ahmadtak-3212/led_cube_project/fpga/led_cube_v1/Galina.srcs/sources_1/new/top_level.sv

`timescale 1ns / 1ps
//////////////////////////////////////////////////////////////////////////////////
// Company: 
// Engineer: 
// 
// Create Date: 01/10/2022 03:30:51 PM
// Design Name: 
// Module Name: top_level
// Project Name: 
// Target Devices: 
// Tool Versions: 
// Description: 
// 
// Dependencies: 
// 
// Revision:
// Revision 0.01 - File Created
// Additional Comments:
// 
//////////////////////////////////////////////////////////////////////////////////

`default_nettype none
module top_level(
        input wire clk_100mhz, 
        input wire btnc,
        input wire [15:0] sw,
        output logic [7:0] ja,
        output logic [7:0] jb,
        output logic [15:0] led 
    );
    logic clk_25mhz;
    clk_wiz_0 clk_wiz(.clk_in(clk_100mhz), .clk_out(clk_25mhz));
    
    logic [3:0][15:0][23:0] led_cube_white;
    assign led_cube_white = 
                  { 
                   {
                    {8'd255, 8'd255, 8'd255}, {8'd255, 8'd255, 8'd255}, {8'd255, 8'd255, 8'd255}, {8'd255, 8'd255, 8'd255},
                    {8'd255, 8'd255, 8'd255}, {8'd255, 8'd255, 8'd255}, {8'd255, 8'd255, 8'd255}, {8'd255, 8'd255, 8'd255},
                    {8'd255, 8'd255, 8'd255}, {8'd255, 8'd255, 8'd255}, {8'd255, 8'd255, 8'd255}, {8'd255, 8'd255, 8'd255},
                    {8'd255, 8'd255, 8'd255}, {8'd255, 8'd255, 8'd255}, {8'd255, 8'd255, 8'd255}, {8'd255, 8'd255, 8'd255}
                   }, 
                   {
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
                   },
                   {
                    {8'd0, 8'd0, 8'd255}, {8'd0, 8'd0, 8'd255}, {8'd0, 8'd0, 8'd255}, {8'd0, 8'd0, 8'd255},
                    {8'd0, 8'd0, 8'd255}, {8'd0, 8'd0, 8'd255}, {8'd0, 8'd0, 8'd255}, {8'd0, 8'd0, 8'd255},
                    {8'd0, 8'd0, 8'd255}, {8'd0, 8'd0, 8'd255}, {8'd0, 8'd0, 8'd255}, {8'd0, 8'd0, 8'd255},
                    {8'd0, 8'd0, 8'd255}, {8'd0, 8'd0, 8'd255}, {8'd0, 8'd0, 8'd255}, {8'd0, 8'd0, 8'd255}
                   }
                 };
                 
   
   logic [1:0] z_level;
   logic [3:0][15:0][23:0] led_cube;
   led_driver_fsm ldf (
      .clk(clk_25mhz), .rst(btnc), .start(btnc), .led_cube(led_cube), 
      .data_out(ja[0]), .data_clk(ja[1]), .data_clr(ja[2]), .sr_wr(ja[3]),
      .pwm_red_out(ja[4]), .pwm_green_out(ja[5]), .pwm_blue_out(ja[6]), .z_level(z_level)  
   );
   always_comb begin 
        case(z_level)
            2'd0: jb[3:0] = 4'b0001;
            2'd1: jb[3:0] = 4'b0010;
            2'd2: jb[3:0] = 4'b0100;
            2'd3: jb[3:0] = 4'b1000;
        endcase
   end 
   logic [31:0] count; 
   logic [1:0] index;
   always_ff @(posedge clk_25mhz) begin
        if(btnc) begin 
            count  <= 0;
            index <= 0;
            led_cube <= led_cube_white;
        end else begin
            if(count >= 4_000_000 - 1) begin
                count <= 0;
                index <= index + 1;
                if(sw[0]) begin
                    case(index) 
                        2'd0 : led_cube <= led_cube_white;
                        2'd1 : led_cube <= led_cube_red;
                        2'd2 : led_cube <= led_cube_green;
                        2'd3 : led_cube <= led_cube_blue;
                    endcase 
                end else begin
                    led_cube <= led_cube_white;
                end               
            end else begin
                count <= count + 1;
            end 
        end     
   end 
   
   assign ja[7] = 0;
   assign jb[7:4] = 0;
   assign led = sw;
endmodule
`default_nettype wire    
