ahmadtak-3212/led_cube_project/fpga/led_cube_v1/Galina.srcs/sources_1/ip/clk_wiz_0/clk_wiz_0_stub.v

// Copyright 1986-2019 Xilinx, Inc. All Rights Reserved.
// --------------------------------------------------------------------------------
// Tool Version: Vivado v.2019.2 (win64) Build 2708876 Wed Nov  6 21:40:23 MST 2019
// Date        : Tue Jan 25 16:43:13 2022
// Host        : DESKTOP-GM0LJJR running 64-bit major release  (build 9200)
// Command     : write_verilog -force -mode synth_stub -rename_top clk_wiz_0 -prefix
//               clk_wiz_0_ clk_wiz_0_stub.v
// Design      : clk_wiz_0
// Purpose     : Stub declaration of top-level module interface
// Device      : xc7a100tcsg324-3
// --------------------------------------------------------------------------------

// This empty module with port declaration file causes synthesis tools to infer a black box for IP.
// The synthesis directives are for Synopsys Synplify support to prevent IO buffer insertion.
// Please paste the declaration into a Verilog source file or add the file as an additional source.
module clk_wiz_0(clk_out, clk_in)
/* synthesis syn_black_box black_box_pad_pin="clk_out,clk_in" */;
  output clk_out;
  input clk_in;
endmodule
